vvip-68/GyverPanelWiFi/Android/arrow-down-blue.png

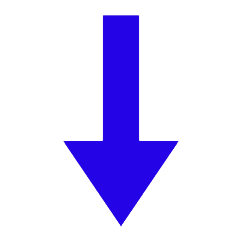
Android/arrow-down-blue.png
