vvip-68/GyverPanelWiFi/Android/arrow-left-blue.png

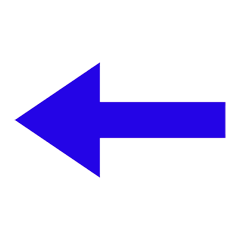
Android/arrow-left-blue.png
