vvip-68/GyverPanelWiFi/Android/arrow-right-blue.png

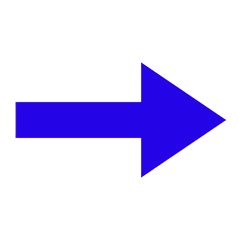
Android/arrow-right-blue.png
