vvip-68/GyverPanelWiFi/Android/arrow-up-blue.png

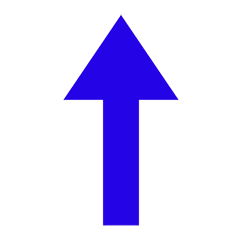
Android/arrow-up-blue.png
