vvip-68/GyverPanelWiFi/Android/g_arkanoid.png

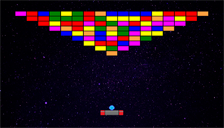
Android/g_arkanoid.png
