vvip-68/GyverPanelWiFi/Android/g_maze.png

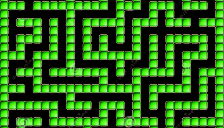
Android/g_maze.png
