vvip-68/GyverPanelWiFi/Android/g_snake.png

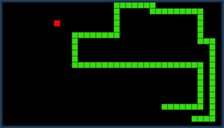
Android/g_snake.png
