vvip-68/GyverPanelWiFi/Android/g_tetris.png

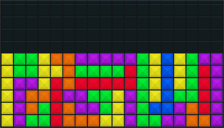
Android/g_tetris.png
