vvip-68/GyverPanelWiFi/Android/joy.png

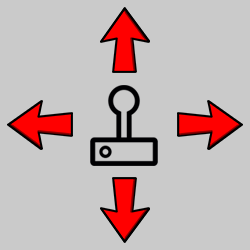
Android/joy.png
