vvip-68/GyverPanelWiFi/Android/LED.png

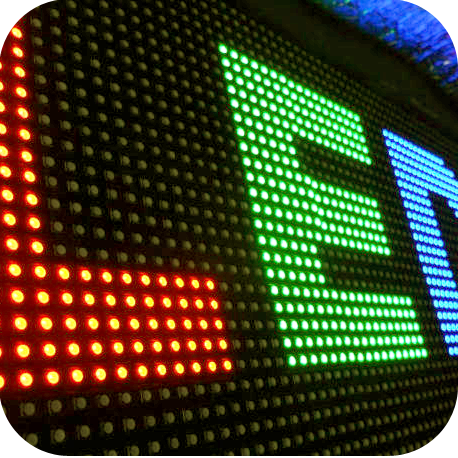
Android/LED.png
