vvip-68/GyverPanelWiFi/Android/menu_bg.png

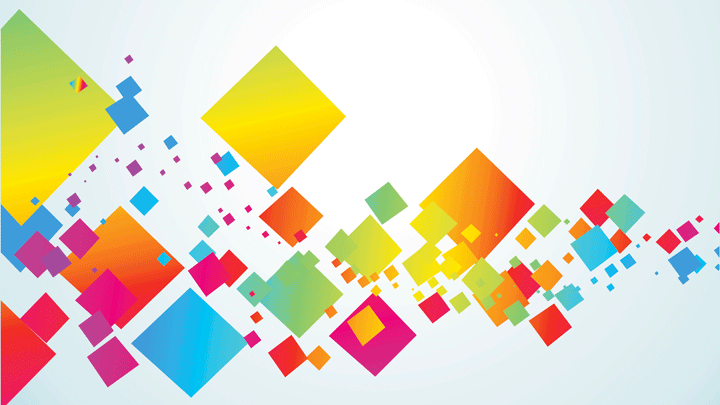
Android/menu_bg.png
