vvip-68/GyverPanelWiFi/schemes/convertor.png

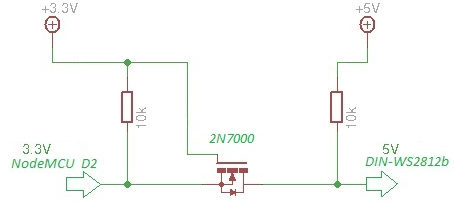
schemes/convertor.png
