vvip-68/GyverPanelWiFi/schemes/nodemcu.png

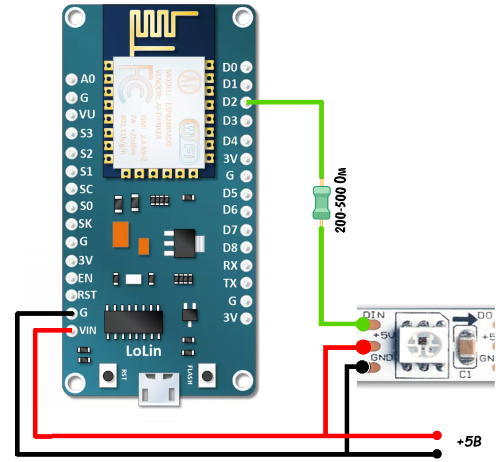
schemes/nodemcu.png
