vvip-68/GyverPanelWiFi/schemes/scheme2.jpg

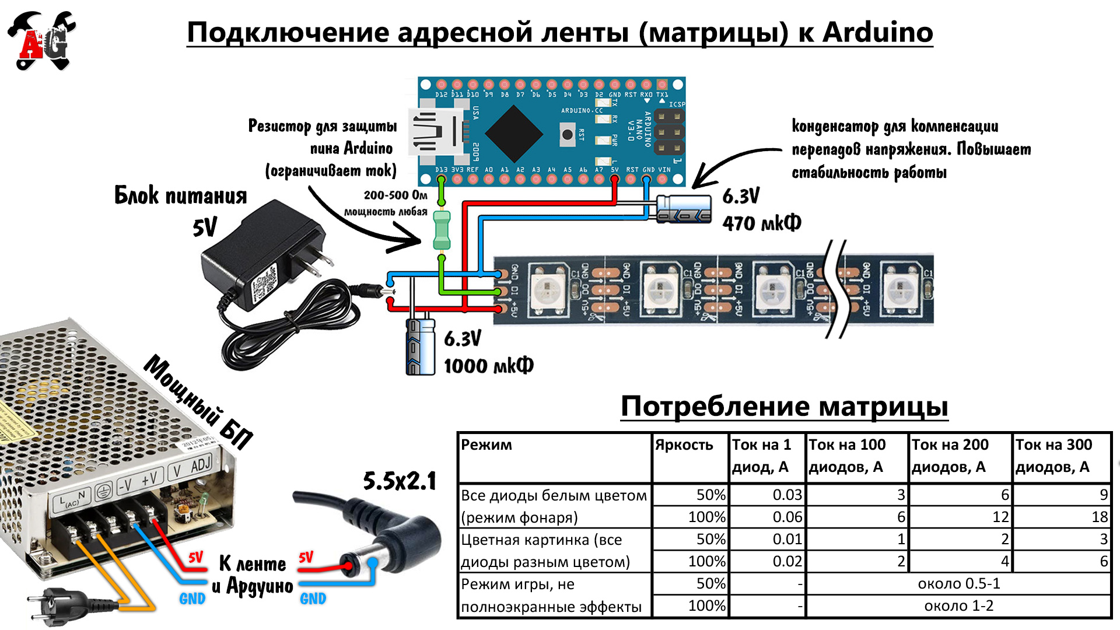
schemes/scheme2.jpg
