vvip-68/GyverPanelWiFi/wiki/About/donate.png

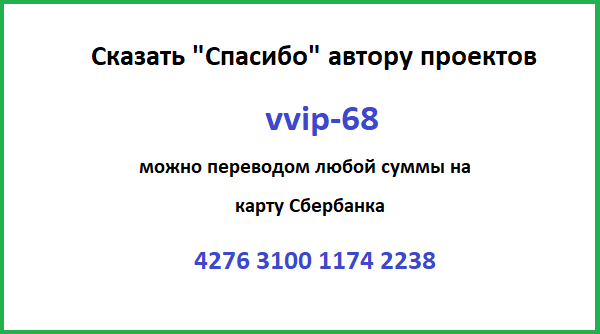
wiki/About/donate.png
