vvip-68/GyverPanelWiFi/wiki/Jinx/video-01.png

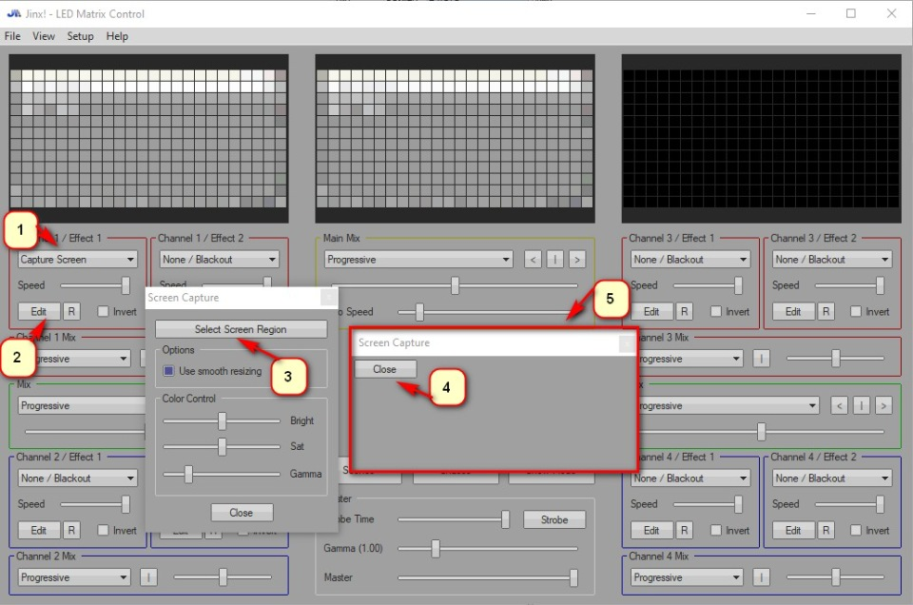
wiki/Jinx/video-01.png
