vvip-68/GyverPanelWiFi/wiki/Jinx/video-02.png

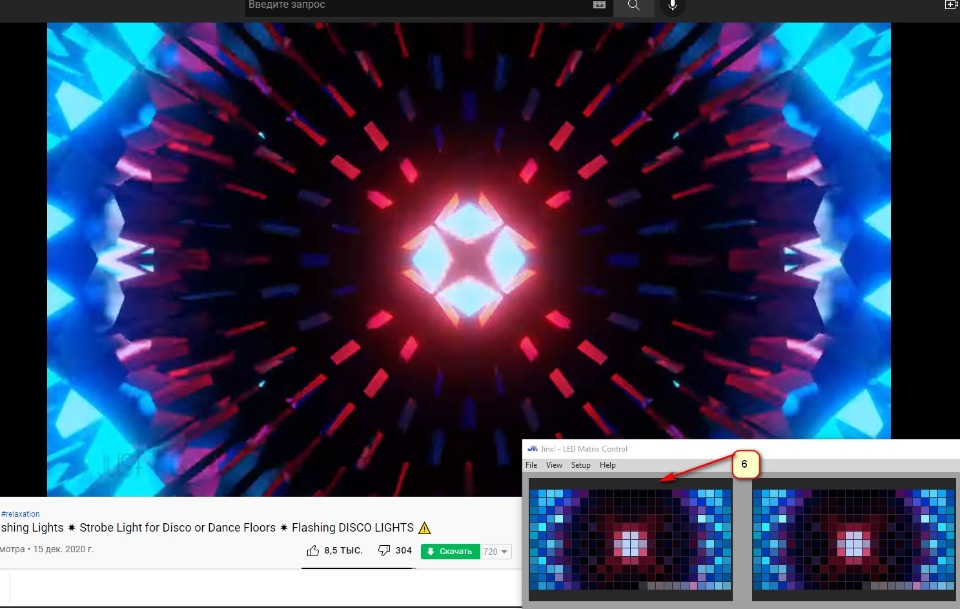
wiki/Jinx/video-02.png
