vvip-68/GyverPanelWiFi/wiki/JinxFramer/screen-09.png

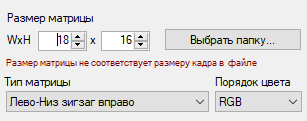
wiki/JinxFramer/screen-09.png
