vvip-68/GyverPanelWiFi/wiki/MQTT/mqtt-09.png

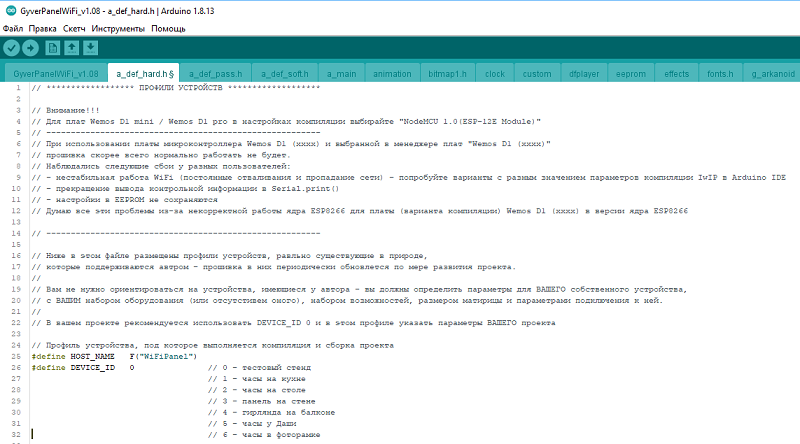
wiki/MQTT/mqtt-09.png
