vvip-68/GyverPanelWiFi/wiki/SD-shield/sd-shield1.jpg

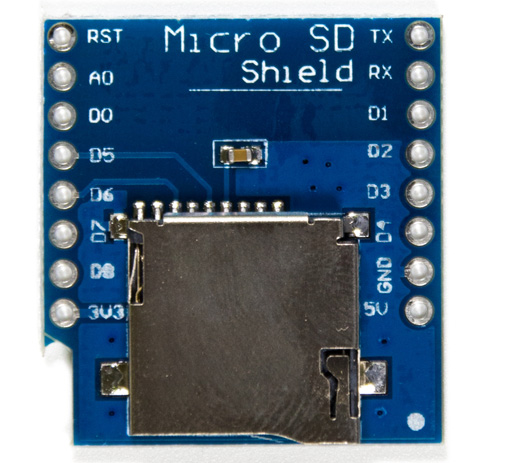
wiki/SD-shield/sd-shield1.jpg
