vvip-68/GyverPanelWiFi/wiki/SD-shield/sd-shield2.jpg

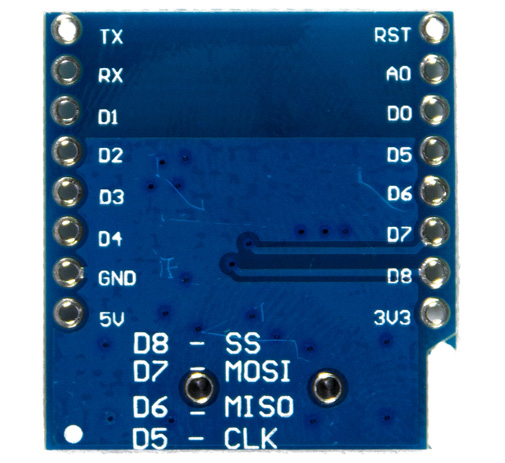
wiki/SD-shield/sd-shield2.jpg
