vvip-68/GyverPanelWiFi/wiki/SD-shield/sd-shield3.jpg

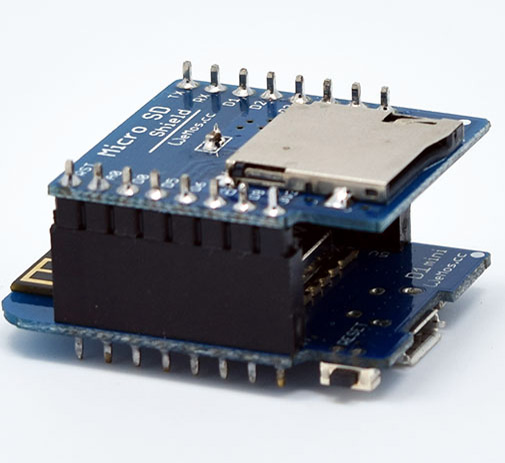
wiki/SD-shield/sd-shield3.jpg
