vvip-68/GyverPanelWiFi/wiki/Tune/p07.png

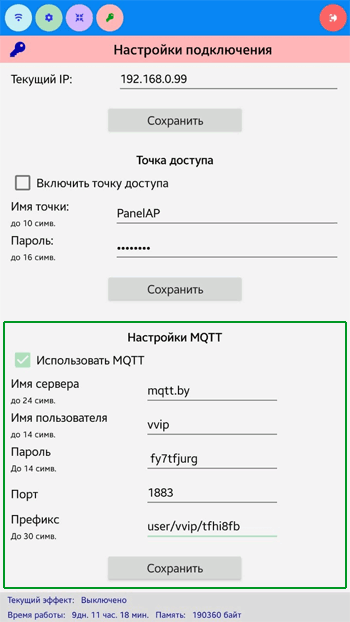
wiki/Tune/p07.png
