vvip-68/GyverPanelWiFi/wiki/Tune/p10.png

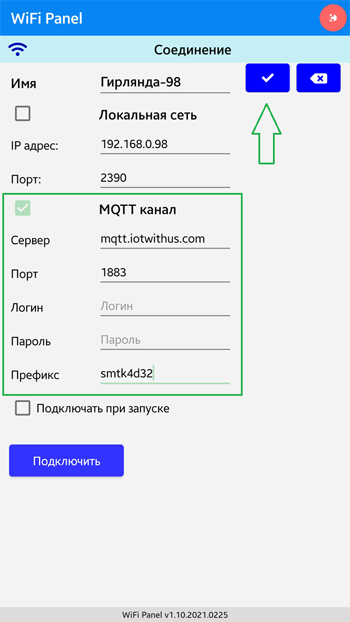
wiki/Tune/p10.png
