vvip-68/GyverPanelWiFi/wiki/Tune/p11.png

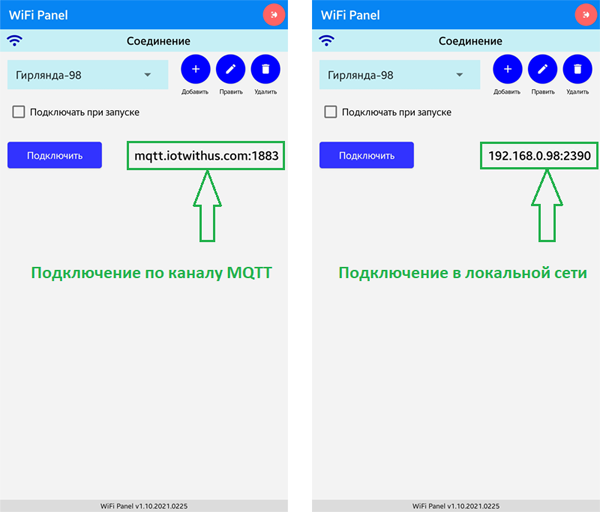
wiki/Tune/p11.png
