vvip-68/GyverPanelWiFi/wiki/Tune/p12-1.png

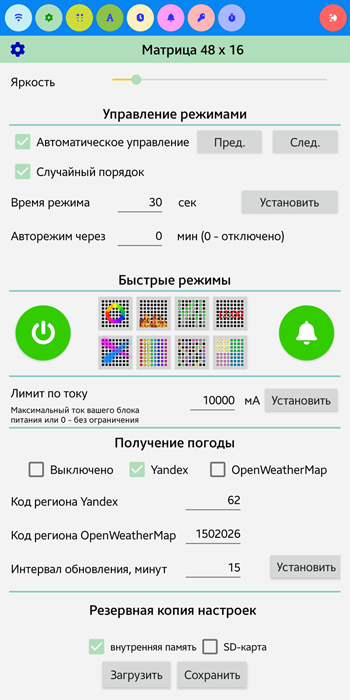
wiki/Tune/p12-1.png
