vvip-68/GyverPanelWiFi/wiki/Tune/p13.png

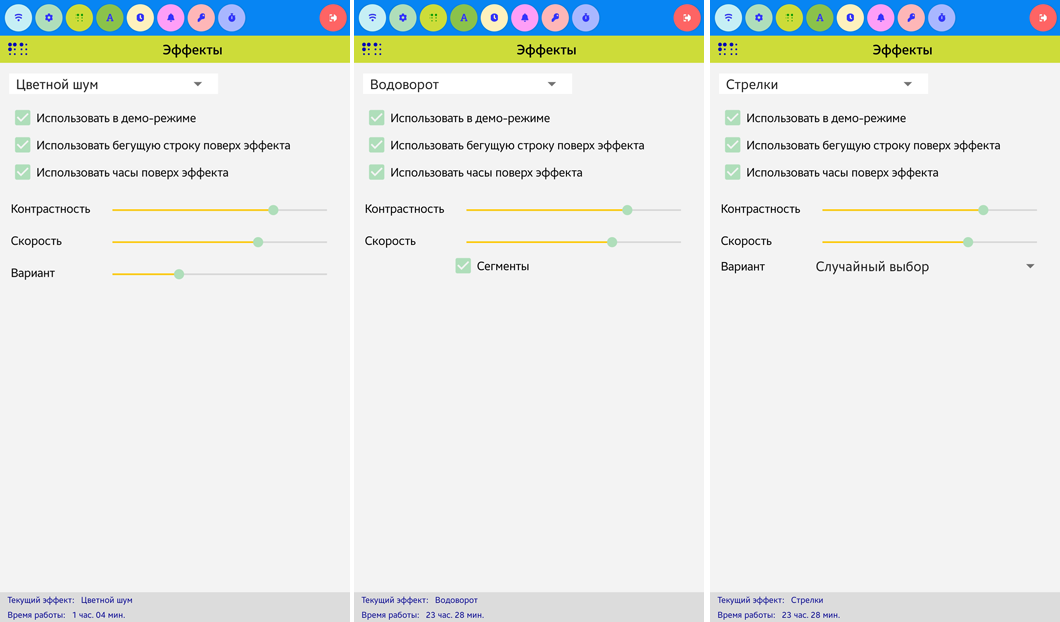
wiki/Tune/p13.png
