vvip-68/GyverPanelWiFi/wiki/Tune/p14.png

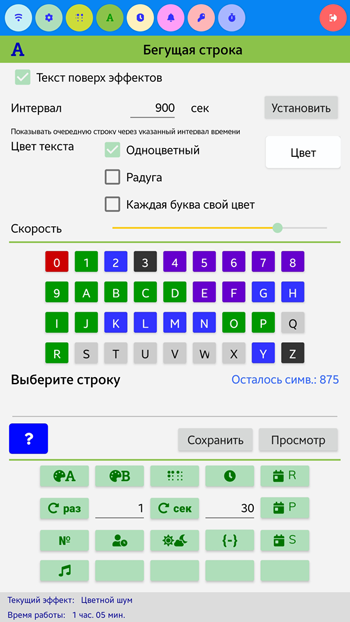
wiki/Tune/p14.png
