vvip-68/GyverPanelWiFi/wiki/Tune/p15.png

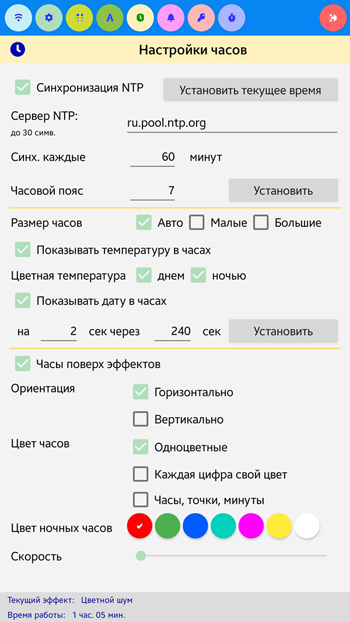
wiki/Tune/p15.png
