vvip-68/GyverPanelWiFi/wiki/Tune/p16-1.png

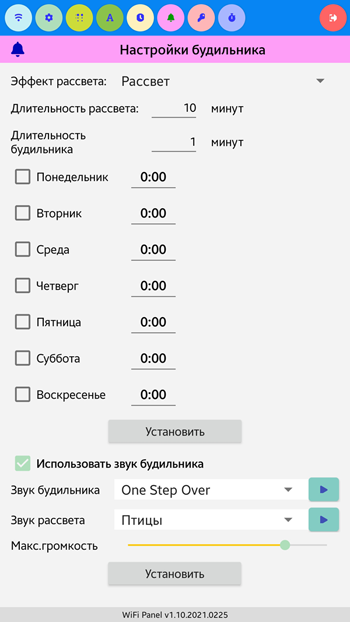
wiki/Tune/p16-1.png
