vvip-68/GyverPanelWiFi/wiki/Tune/p16-2.png

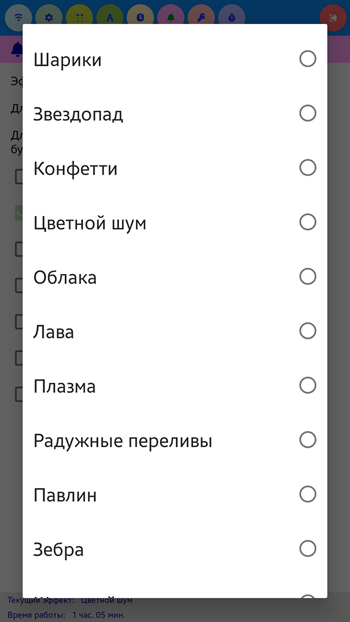
wiki/Tune/p16-2.png
