vvip-68/GyverPanelWiFi/wiki/Tune/p16-3.png

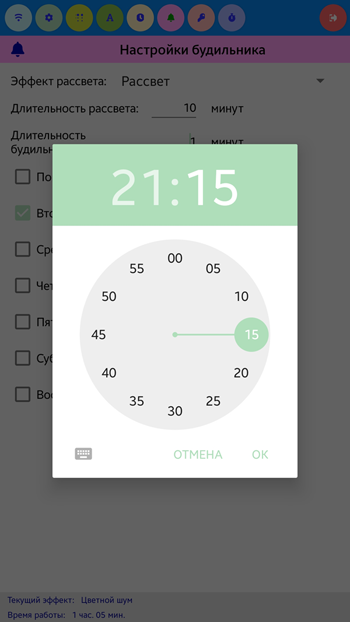
wiki/Tune/p16-3.png
