vvip-68/GyverPanelWiFi/wiki/Tune/p17-1.png

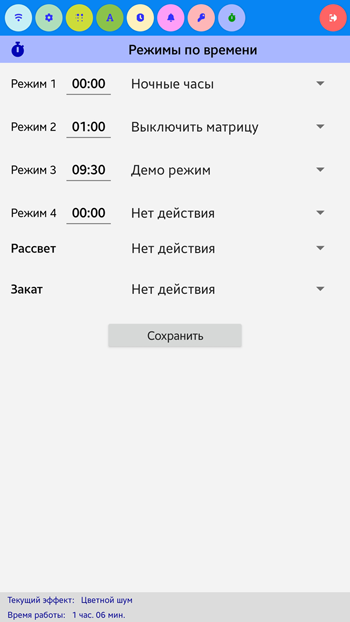
wiki/Tune/p17-1.png
