vvip-68/GyverPanelWiFi/wiki/Tune/p17-2.png

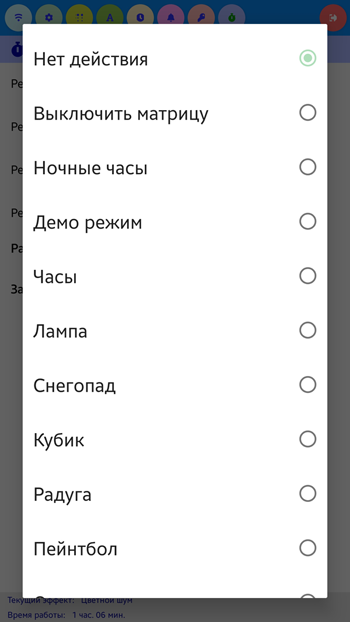
wiki/Tune/p17-2.png
