vvip-68/GyverPanelWiFi/firmware/GyverPanelWiFi_v1.13/pictures.ino

// *************************** КАРТИНКИ (СЛАЙДЫ) ****************************
//
// Поиск картинок, пригодных для эффекта "Слайды":
//   1. Если доступна SD-карта - ищем картинки на ней, сначала в папке с размерами WxH
//   2. Если картинки не найдены - ищем картинки в файловой системе МК, сначала в папке с размерами WxH
//   3. Если картинки не найдены и доступна SD-карта - ищем картинки на ней, в папке с размерами 16x16
//   4. Если картинки не найдены - ищем картинки в файловой системе МК,  в папке с размерами 16x16
//   5. Если картинки не найдены - слайды 16x16 будем брать из эффекта анимации "Погода" - там 20 фреймов - 20 картинок 16x16
//
// Картинки для эффекта "Слайды" могут быть подготовлены в приложении JinxFramer или нарисованы на самой матрице 
// используя приложение управления матрицей WiFiPlayer
//
// Подготовленные картинки должны быть помещены а папку 'data' скетча, внутрь папки "WpH" - где W - ширина матрицы и H - высота матрицы.
// Так, для полного размера матрицы 24 x 18 имя папки должно быть "24p18" и в ней - подготовленные картинки размером 24x18
// 
// Для примера в папке дата размещена папка 16p16 и в ней набор картинок "от автора".
// Если папка с размерами картинок под вашу матрицу не будет найдена микроконтроллером - для эффекта будут смпользованы картинки 16x16
// из папки с примерами "16p16";
//
// Если и папка папка с примерами "16p16" также не будет найдена, для эффекта будут смпользованы картинки 16x16 из анимации "Погода".
//
// Для загрузки файлов в файловую систему микроконтроллера используется плагин к Arduino IDE, который находится в папке проекта tools/LittleFS_Uploader
// Инструкция по установки плагина в IDE и подсказки к использованию - в файле readme.txt в той же папке
//
// Если размеры картинки слайда меньше размера матрицы на 6 пикселей - она будет плавно перемещаться по полю матрицы.
// Скорость перемещения задается слайдером "Вариант". В крайнем левом положении слайдера картинка не перемещается и выводится по центру поля матрицы
//
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
